famibelle/PlayMoDrone/PCB/PlaymoDrone_etch_silk_bottom.pdf

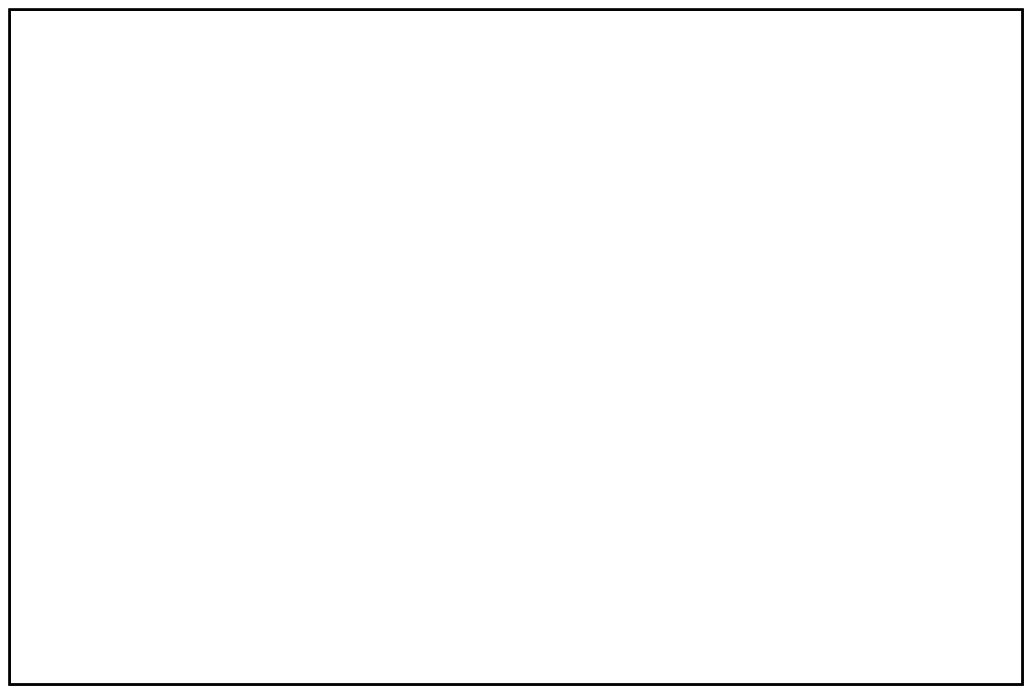
[picture p7: page 1]
