famibelle/PlayMoDrone/PCB/PlaymoDrone_etch_silk_top.pdf

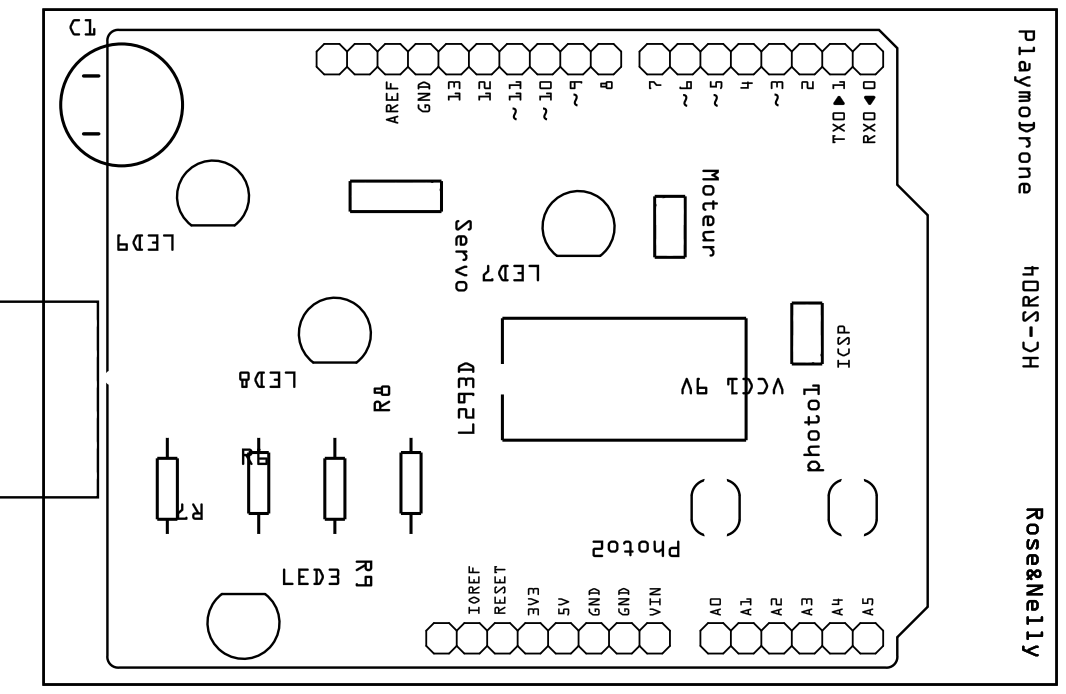
[picture p12: page 1]
