famibelle/PlayMoDrone/PCB/PlaymoDrone_etch_silk_top_mirror.pdf

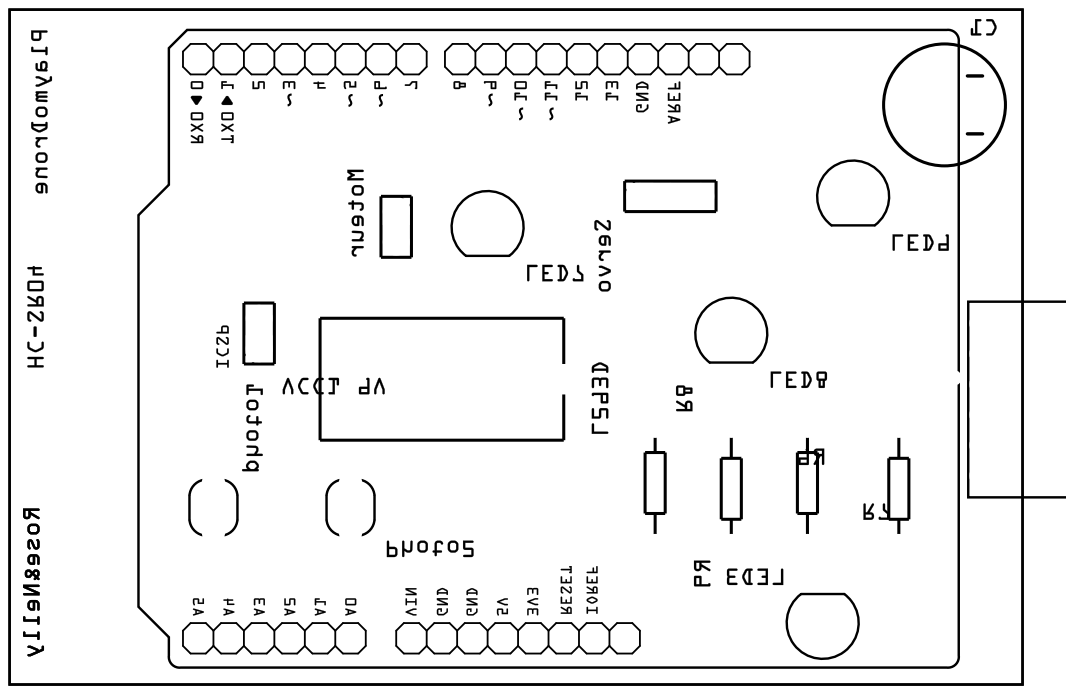
[picture p13: page 1]
